Tora0615/SABERSTAFF-01/02.Software/v1.3_simple_attiny_ver/define_table.ino

//火焰樣式
#define FIRENORNAL 0
#define FIREPURPLE 1
#define FIRESKYBLUE 2

//彩虹樣式
#define RAINBOWSIMILAR 0
#define RAINBOWDISTRIBUTED 1

//速度
#define SLOW 0
#define MID 1
#define FAST 2
#define VERYFAST 3

//顏色
#define RED 0
#define SKYBLUE 1
#define PURPLE 2
#define GREEN 3
#define BLUE 4
#define YELLOW 5
#define BLACK 10
#define WHITE 11

//亮度
#define NIGHT 0
#define DAWN 1
#define NOON 2
